antmicro/d1600e-psu-breakout/assets/previews/layer1.png

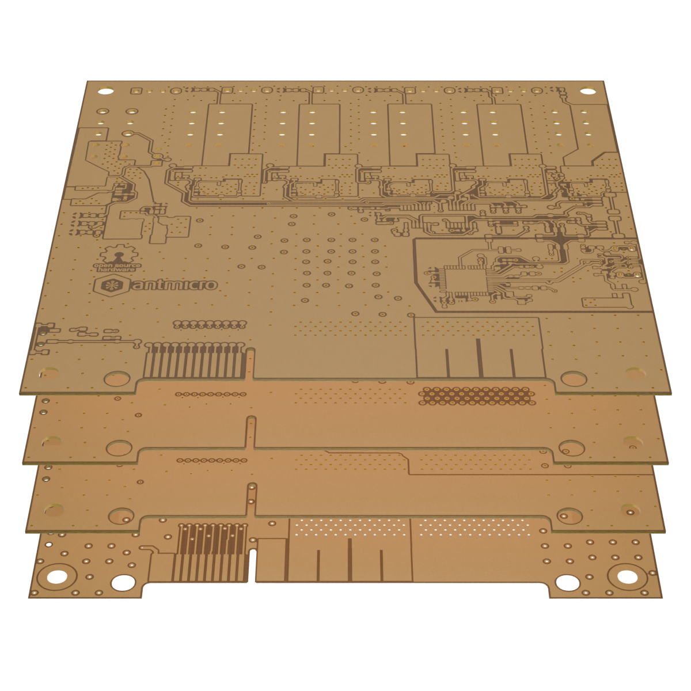
assets/previews/layer1.png
