antmicro/d1600e-psu-breakout/assets/previews/layer1_thumbnail.png

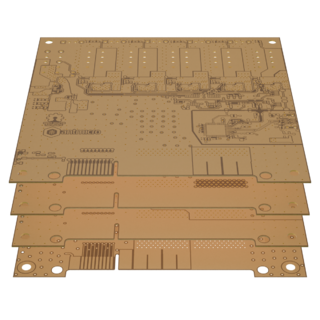
assets/previews/layer1_thumbnail.png
