antmicro/d1600e-psu-breakout/assets/previews/layer2.png

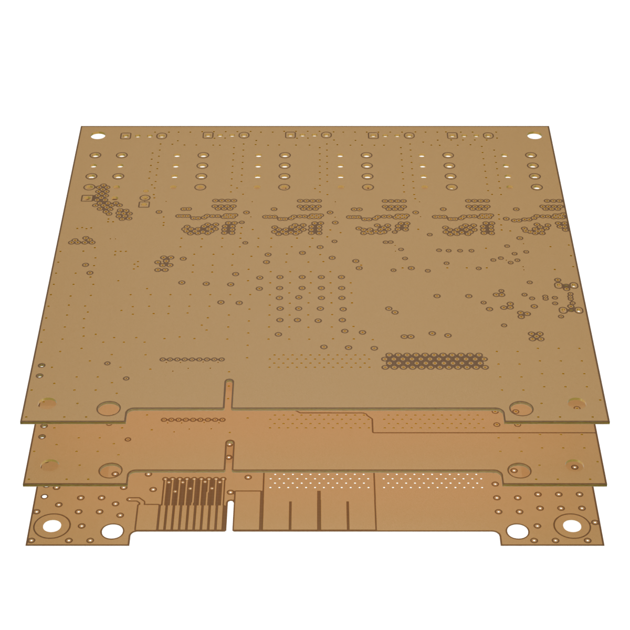
assets/previews/layer2.png
