antmicro/d1600e-psu-breakout/assets/previews/layer2_thumbnail.png

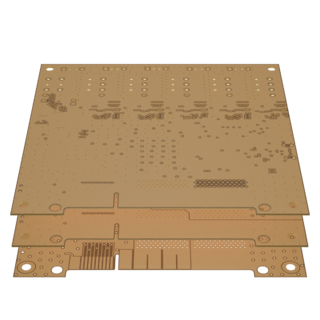
assets/previews/layer2_thumbnail.png
