antmicro/d1600e-psu-breakout/assets/previews/layer3.png

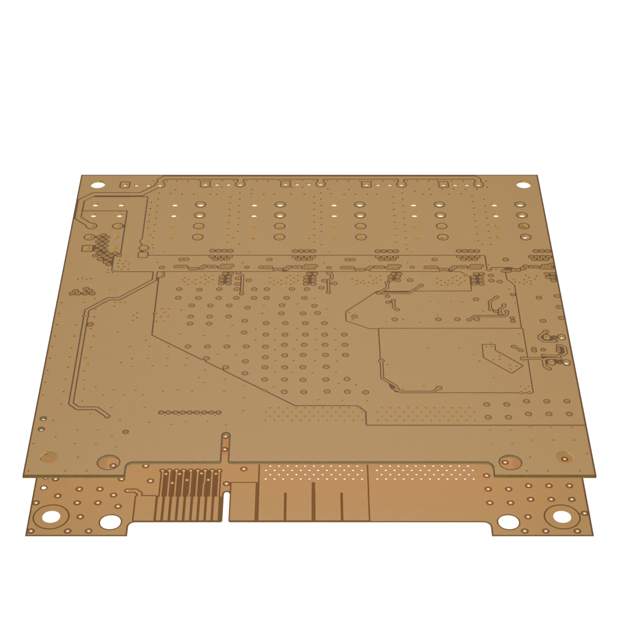
assets/previews/layer3.png
