antmicro/d1600e-psu-breakout/assets/previews/layer3_thumbnail.png

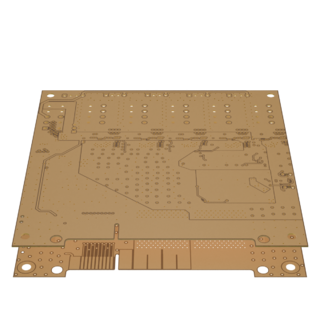
assets/previews/layer3_thumbnail.png
