antmicro/d1600e-psu-breakout/assets/previews/layer4.png

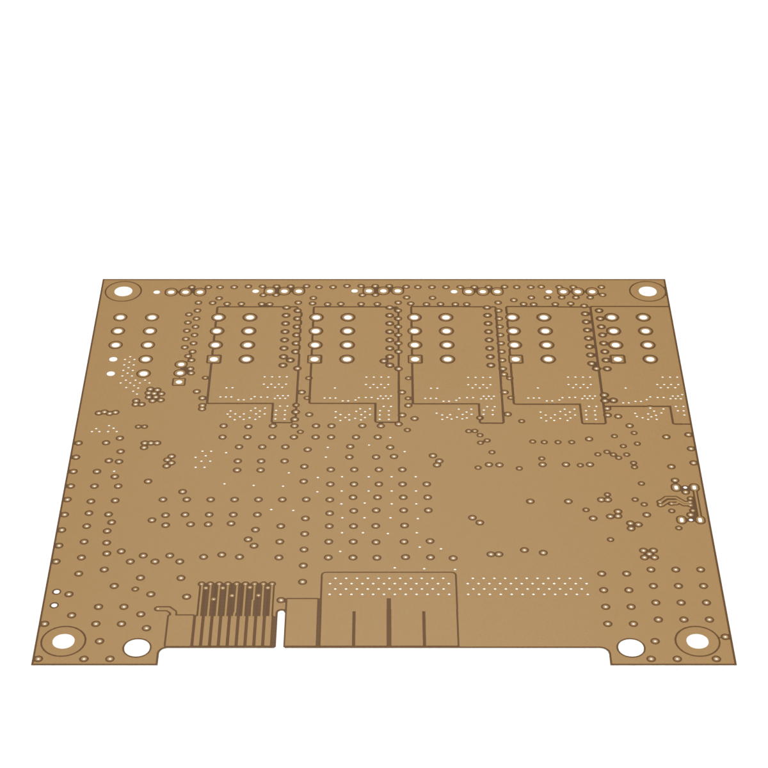
assets/previews/layer4.png
