antmicro/d1600e-psu-breakout/assets/previews/layer4.webp

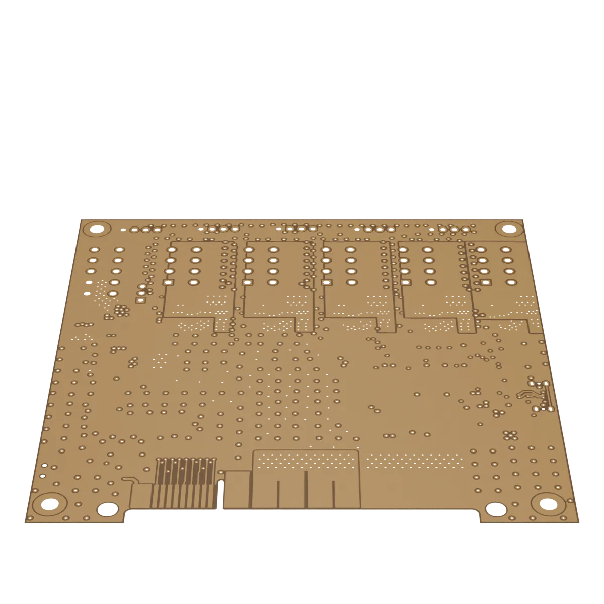
assets/previews/layer4.webp
