antmicro/d1600e-psu-breakout/assets/previews/layer4_thumbnail.png

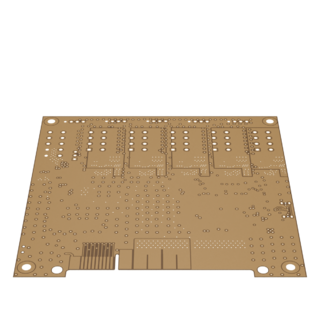
assets/previews/layer4_thumbnail.png
