antmicro/d1600e-psu-breakout/assets/previews/leftB.png

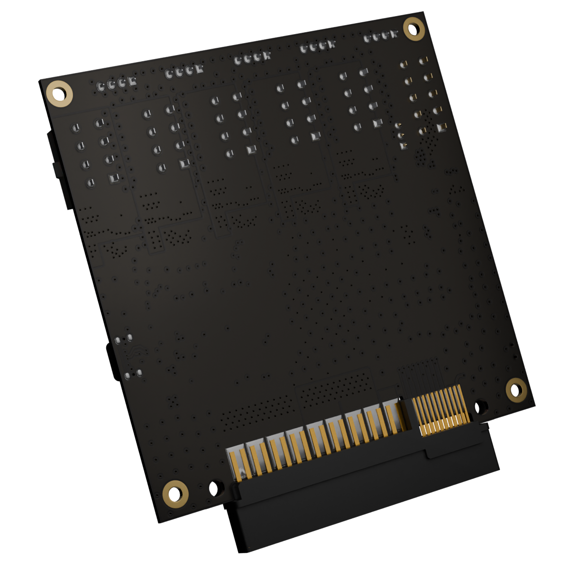
assets/previews/leftB.png
