antmicro/d1600e-psu-breakout/assets/previews/leftT.png

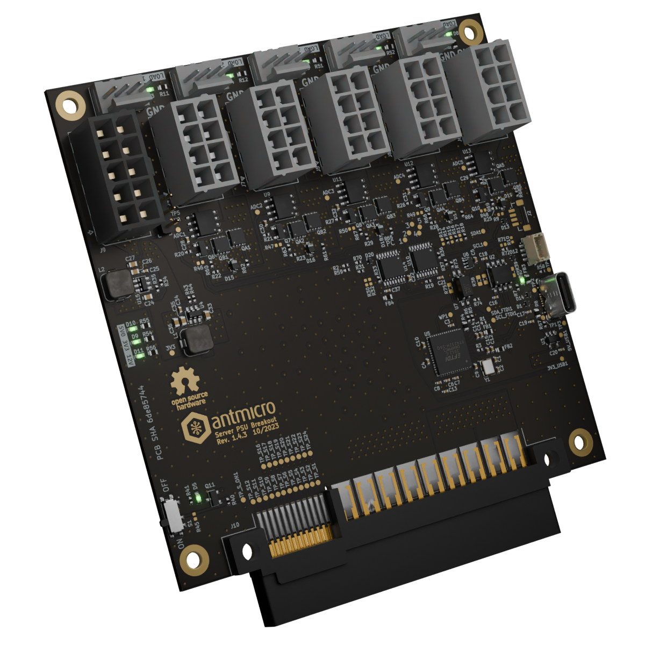
assets/previews/leftT.png
