antmicro/d1600e-psu-breakout/assets/previews/orthoB.png

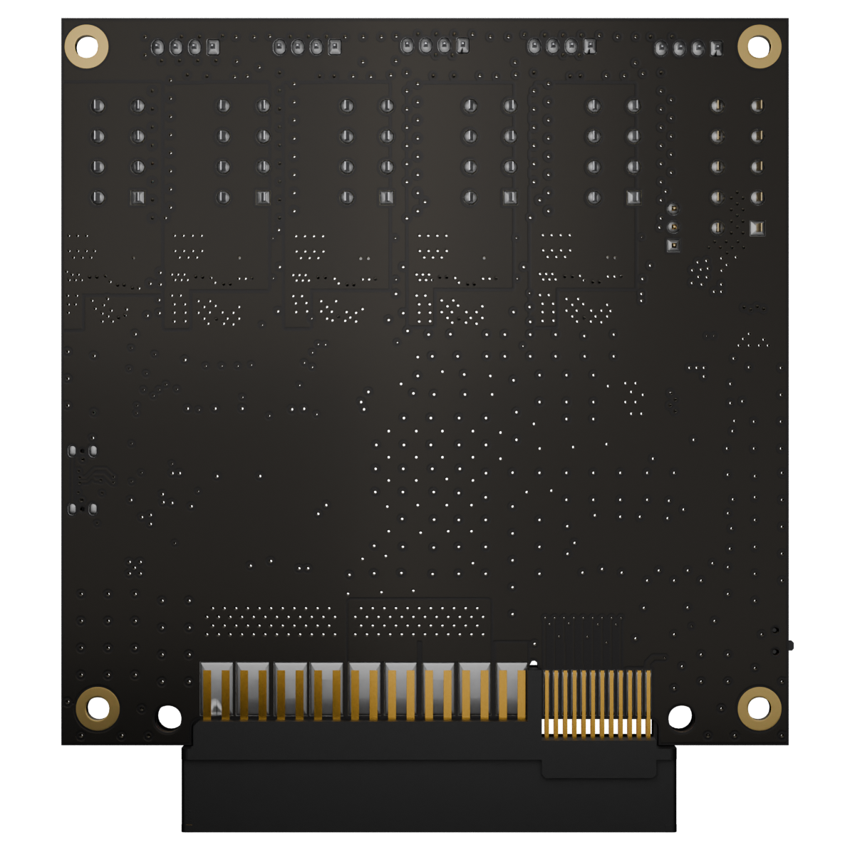
assets/previews/orthoB.png
