antmicro/d1600e-psu-breakout/assets/previews/orthoB_photo.webp

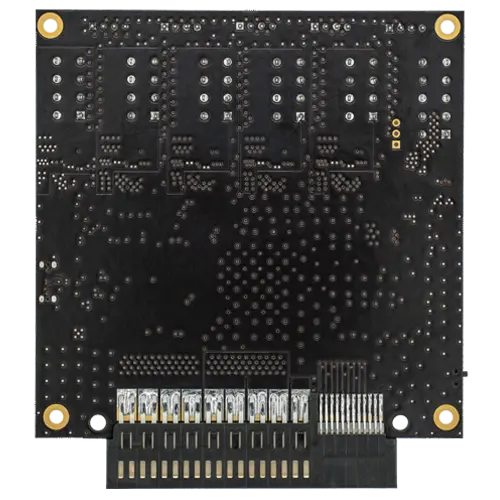
assets/previews/orthoB_photo.webp
