antmicro/d1600e-psu-breakout/assets/previews/orthoT.png

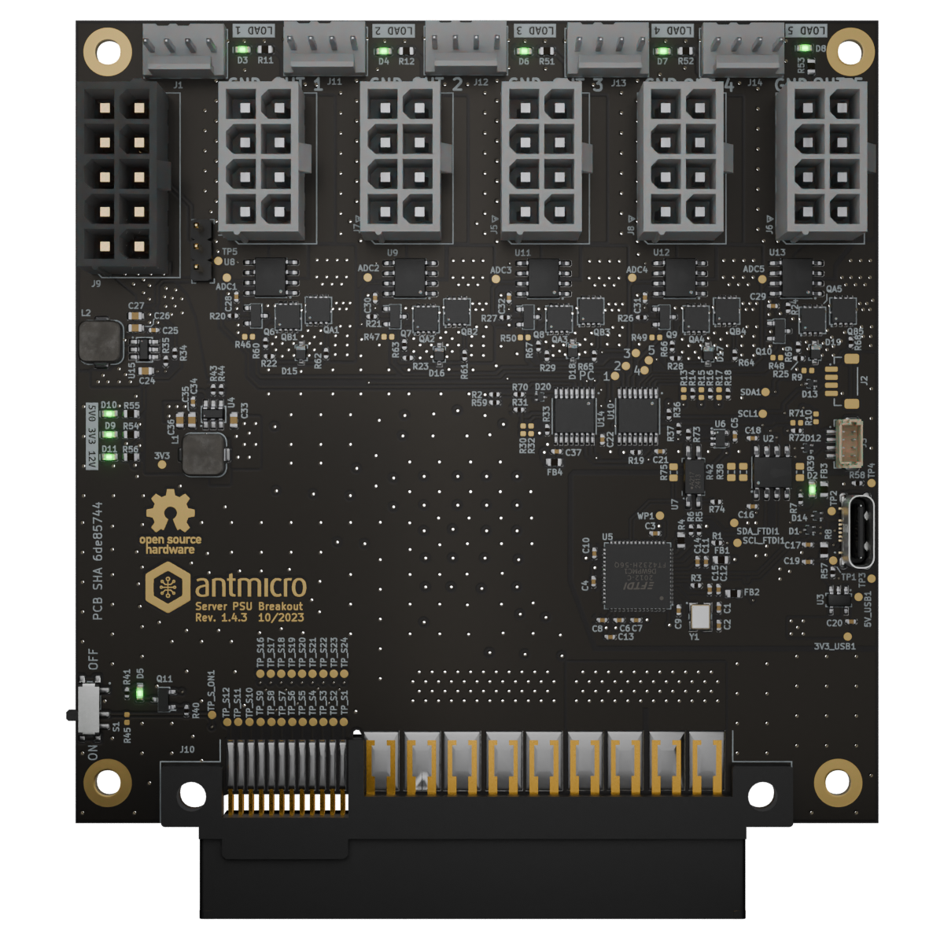
assets/previews/orthoT.png
