antmicro/d1600e-psu-breakout/assets/previews/orthoT_photo.webp

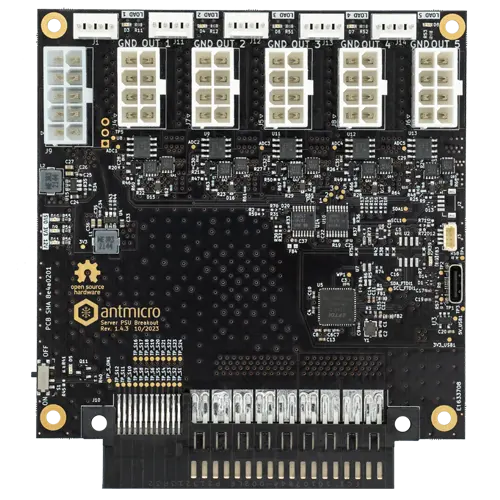
assets/previews/orthoT_photo.webp
