antmicro/d1600e-psu-breakout/assets/previews/rightB.png

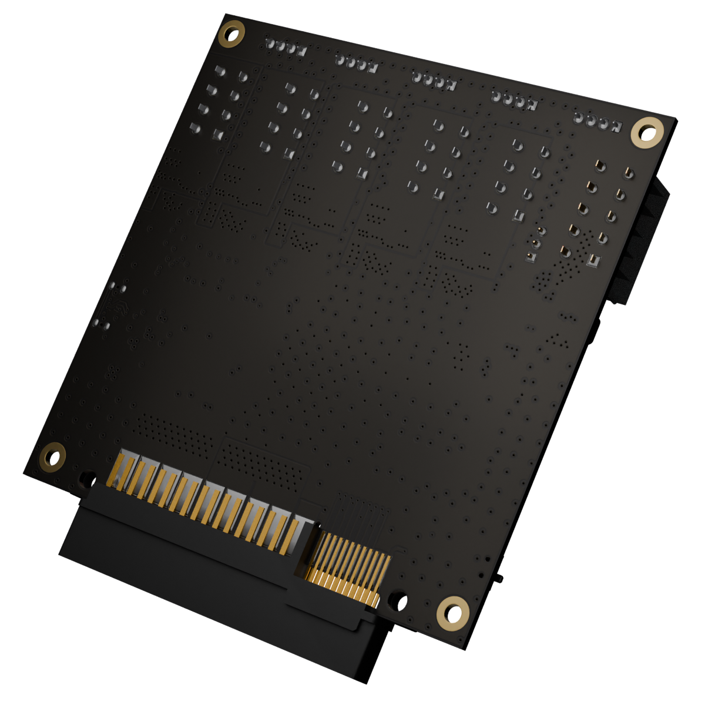
assets/previews/rightB.png
