antmicro/d1600e-psu-breakout/assets/previews/rightT.png

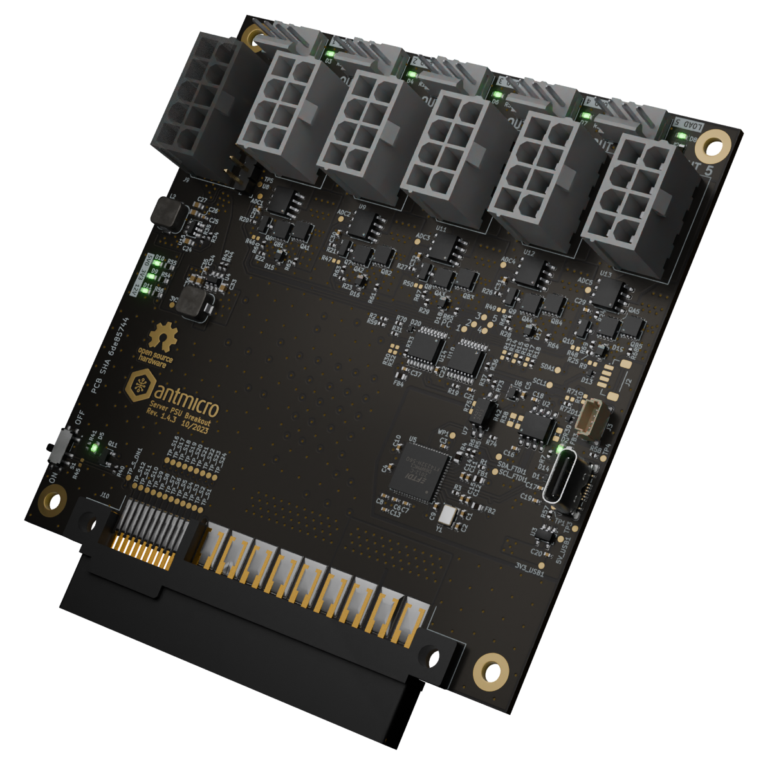
assets/previews/rightT.png
