antmicro/d1600e-psu-breakout/assets/wireframe/wireframe_descriptions_bottom.png

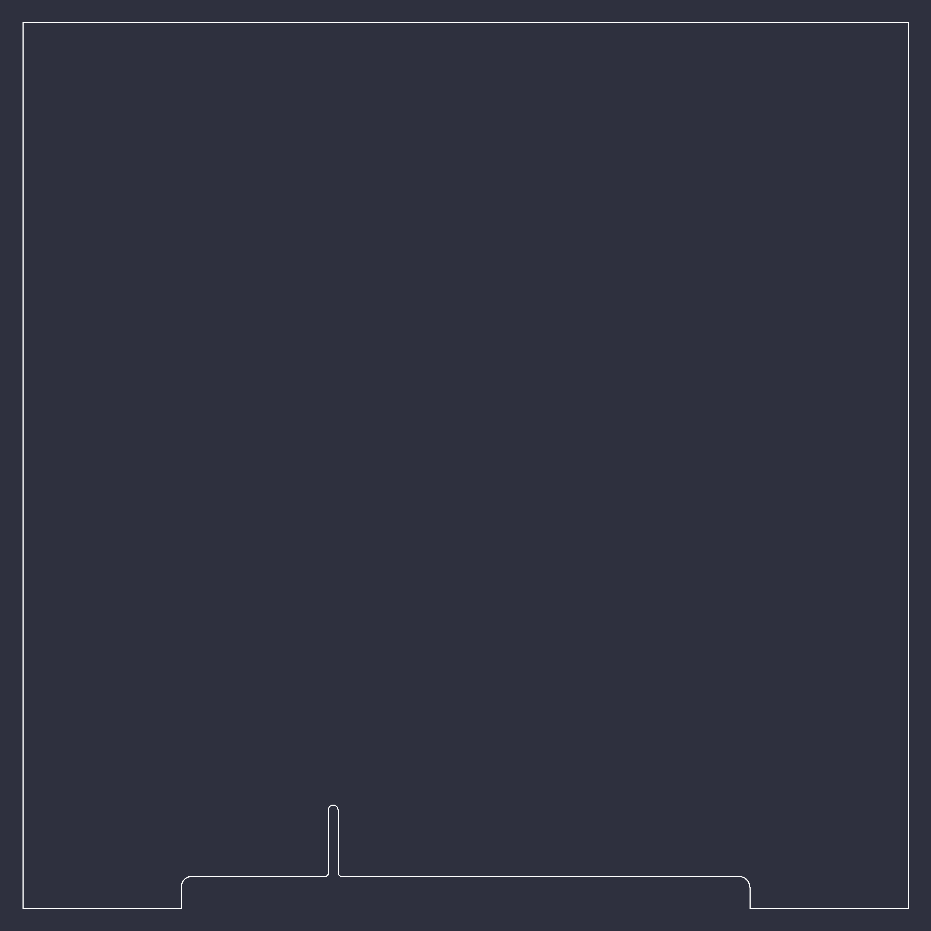
assets/wireframe/wireframe_descriptions_bottom.png
