antmicro/d1600e-psu-breakout/assets/wireframe/wireframe_descriptions_top.png

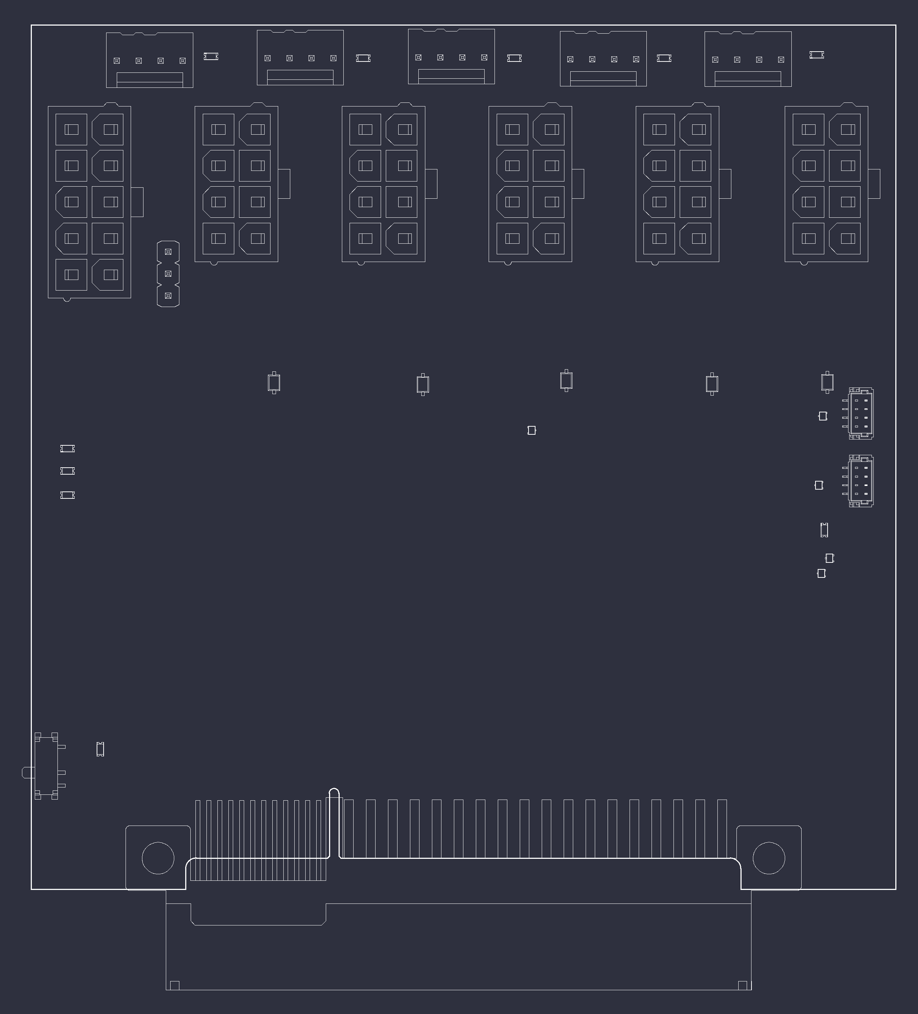
assets/wireframe/wireframe_descriptions_top.png
