antmicro/d1600e-psu-breakout/assets/wireframe/wireframe_dimensions.png

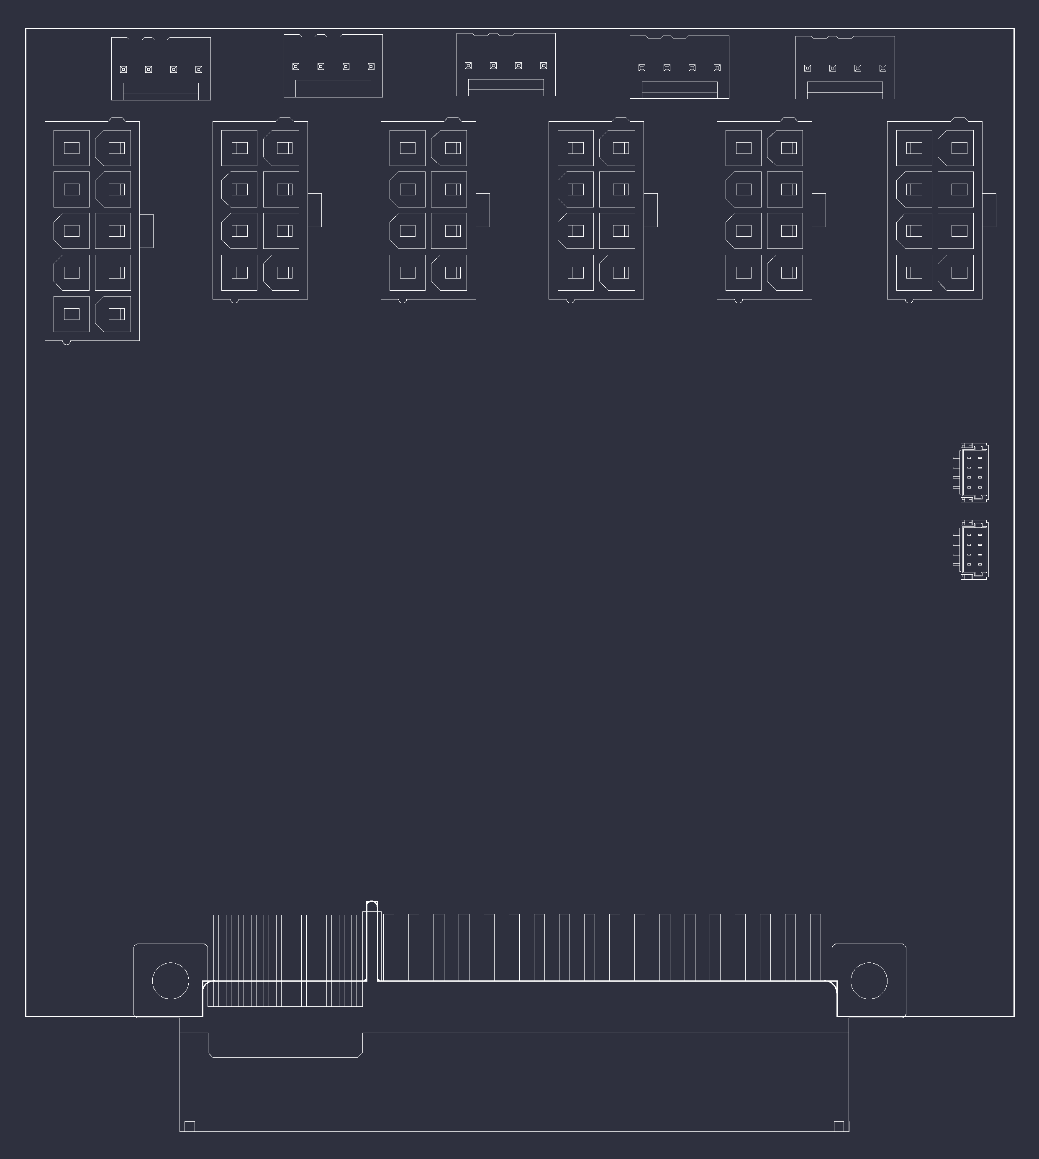
assets/wireframe/wireframe_dimensions.png
